Giorgiolag/Odysseus-A-new-educational-robotic-kit/Hardware/plastic_parts/plastic parts step files/top_motors.step

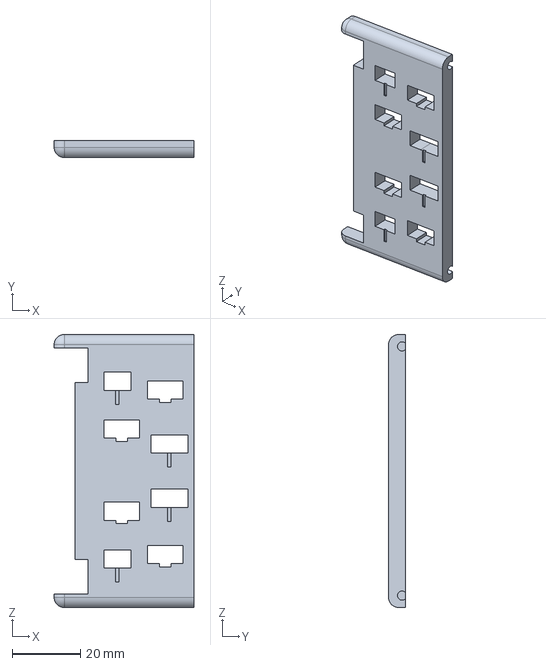
[picture p32: CAD file, 2025-08-25]
Hardware/plastic_parts/plastic parts step files/top_motors.step
41.0 x 5.00 x 80.0 mm
