Giorgiolag/Odysseus-A-new-educational-robotic-kit/Hardware/plastic_parts/plastic parts step files/switch_middle.step

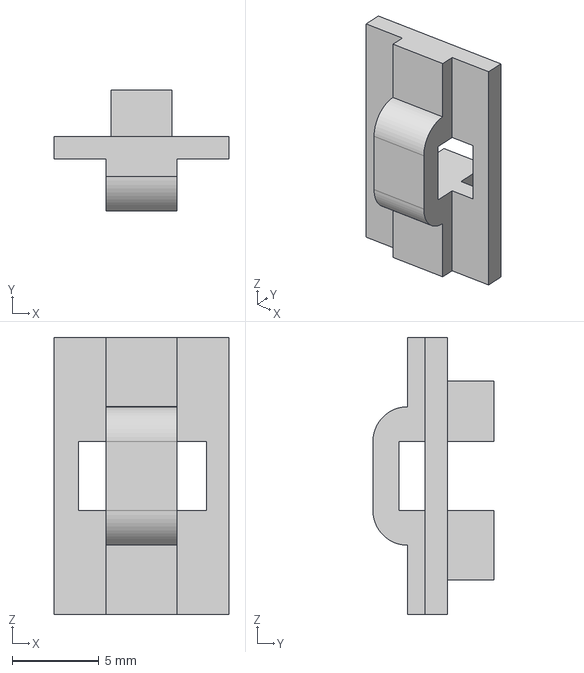
[picture p33: CAD file, 2025-08-25]
Hardware/plastic_parts/plastic parts step files/switch_middle.step
10.1 x 7.00 x 16.0 mm
