Giorgiolag/Odysseus-A-new-educational-robotic-kit/Hardware/plastic_parts/plastic parts step files/door.step

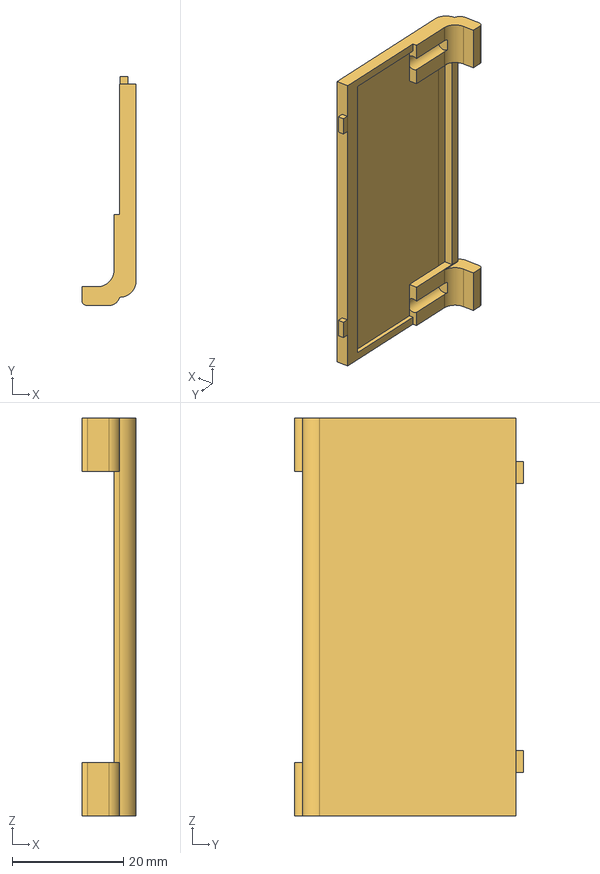
[picture p34: CAD file, 2025-08-25]
Hardware/plastic_parts/plastic parts step files/door.step
9.80 x 41.2 x 71.6 mm
