Giorgiolag/Odysseus-A-new-educational-robotic-kit/Hardware/plastic_parts/plastic parts step files/side_cover.step

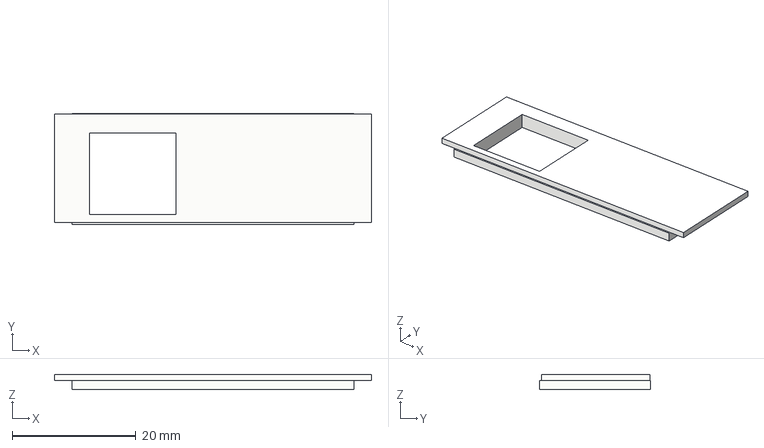
[picture p35: CAD file, 2025-08-25]
Hardware/plastic_parts/plastic parts step files/side_cover.step
51.2 x 17.9 x 2.50 mm
