Giorgiolag/Odysseus-A-new-educational-robotic-kit/Hardware/plastic_parts/plastic parts step files/bottom.step

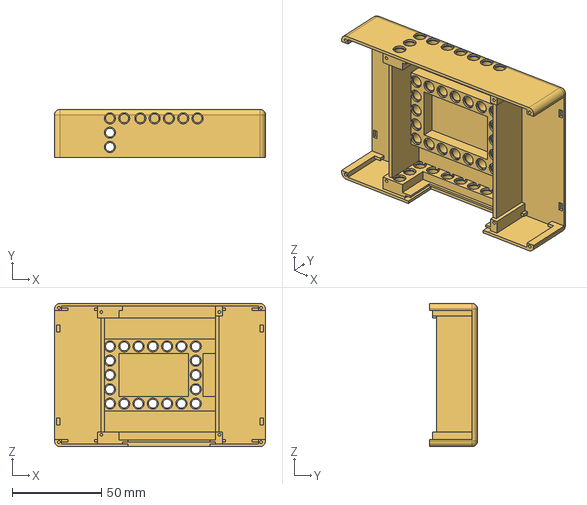
[picture p36: CAD file, 2025-08-25]
Hardware/plastic_parts/plastic parts step files/bottom.step
118.0 x 26.9 x 80.0 mm
