Giorgiolag/Odysseus-A-new-educational-robotic-kit/Hardware/plastic_parts/plastic parts step files/mid.step

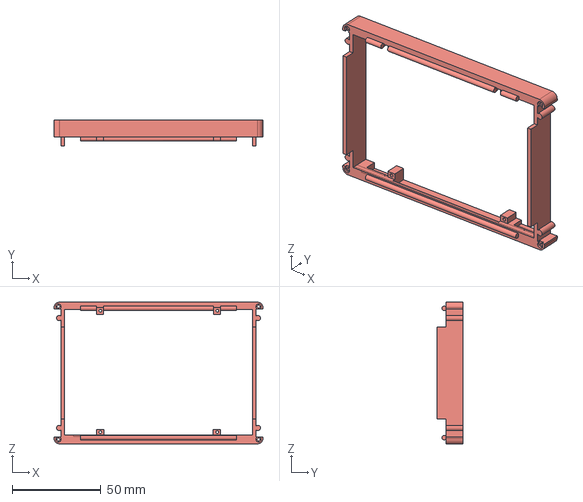
[picture p37: CAD file, 2025-08-25]
Hardware/plastic_parts/plastic parts step files/mid.step
118.0 x 14.6 x 80.0 mm
