Giorgiolag/Odysseus-A-new-educational-robotic-kit/Hardware/plastic_parts/plastic parts step files/top_sensors.step

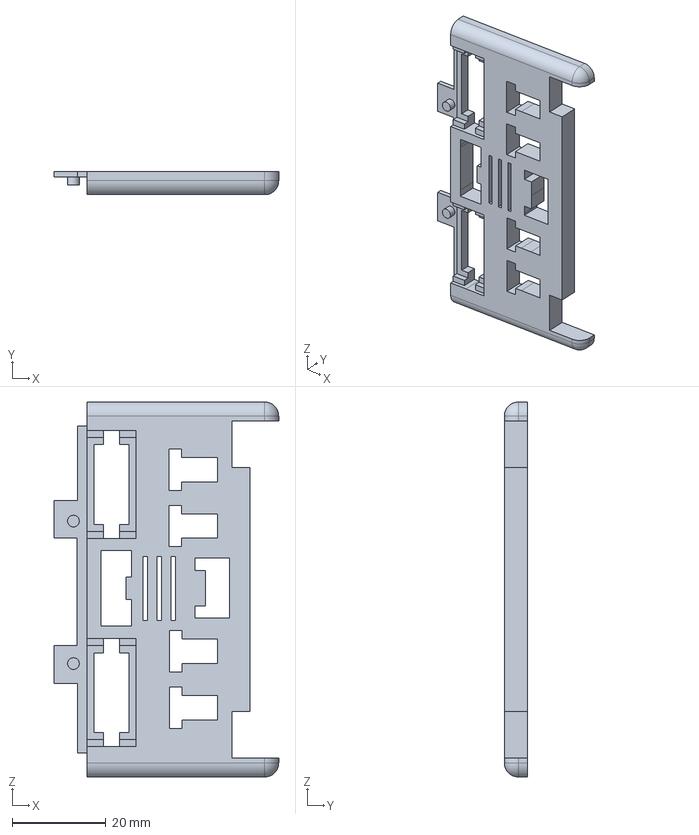
[picture p38: CAD file, 2025-08-25]
Hardware/plastic_parts/plastic parts step files/top_sensors.step
47.9 x 5.00 x 80.0 mm
